eldrichrebello/opqbox2/Schematics/LtSpice/DCDC.asc

C1: cap; 33pF
C2: cap; 330p
C3: cap; 22µF
C4: cap; 100µF
L1: ind; 10µ
R1: res; 649k
R2: res; 162k
R3: res; 10k
R4: res; 15k
R5: res; 15
R6: res; 500k
R7: res; 900k
U1: LTC3534
U2: LT1017
V1: voltage; PWL(0 5 2m 5 3m 3.2 5m 2.7)
V2: voltage; 1.8V
Named nets: 0, Vin, Vout
.tran 0 25m 0
