eldrichrebello/opqbox2/Software/Triggering/src/LocalAnalysis.cpp

#include "LocalAnalysis.hpp"
#include "opqdata.hpp"
#include "Settings.hpp"

#include <math.h>
#include <algorithm>
#include <iostream>
#include <opqdata.hpp>
#include "RedisSerializer.hpp"
#include <boost/log/trivial.hpp>
using namespace opq;
using namespace opq::data;
using namespace std;

LocalAnalysis::LocalAnalysis(opq::data::MeasurementQueue inQ, opq::data::AnalysisQueue outQ) {
    _inQ = inQ;
    _outQ = outQ;
    _state = INITIALIZING_DOWNSAMPLING_FILTER;
    AntialiasDownsamplingFilter_init(&adf);
    LowPassFilter_init(&lpf);
}

void LocalAnalysis::loop(bool &running) {
    auto settings = Settings::Instance();
    float calConstant = settings->getFloat("acquisition_calibration_constant");

    RedisSerializer redis;
    BOOST_LOG_TRIVIAL(info) << "Analysis filter setup....";
    while (running) {
        opq::data::OPQMeasurementPtr measurement = _inQ->pop();
        if (_state != RUNNING) {
            initFilter(measurement);
            continue;
        }
        opq::data::OPQAnalysisPtr analysis = opq::data::make_analysis();
        _downSampled.clear();

        analysis->RMS = 0;
        for (auto &&frame : measurement->cycles) {
            analysis->RMS += rmsVoltage(frame.data);

            for (int i = 0; i < SAMPLES_PER_CYCLE; i++) {
                AntialiasDownsamplingFilter_put(&adf, frame.data[i]);
                if (i % DECIMATION_FACTOR == 0) {
                    float antialiased_value = AntialiasDownsamplingFilter_get(&adf);
                    LowPassFilter_put(&lpf, antialiased_value);
                    _downSampled.push_back(LowPassFilter_get(&lpf));
                }
            }
        }

        analysis->start = measurement->timestamps[0];
        analysis->RMS /= measurement->cycles.size();
        analysis->RMS /= calConstant;

        std::vector<float> zeroCrossings;
        float last = FP_NAN;
        float next = 0;
        for (size_t i = 0; i < _downSampled.size(); i++) {
            if (last != FP_NAN) {
                if ((last <= 0 && _downSampled[i] > 0) || (last < 0 && _downSampled[i] >= 0)) {
                    next = _downSampled[i];
                    zeroCrossings.push_back(1.0f * i - (next) / (next - last));
                }
            }
            last = _downSampled[i];
        }

        float accumulator = 0;
        for (size_t i = 1; i < zeroCrossings.size(); i++) {
            accumulator += zeroCrossings[i] - zeroCrossings[i - 1];
        }
        accumulator /= zeroCrossings.size() - 1;
        analysis->frequency = SAMPLES_PER_CYCLE *
                              CYCLES_PER_SEC /
                              DECIMATION_FACTOR /
                              accumulator;

        analysis->start = measurement->timestamps.front();
        analysis->current_counter = measurement->cycles[measurement->cycles.size() - 1].current_counter;
        analysis->last_gps_counter = measurement->cycles[measurement->cycles.size() - 1].last_gps_counter;
        analysis->flags = 0;
        for (auto &&frame : measurement->cycles) {
            analysis->flags |= frame.flags;
        }
        _outQ->push(analysis);
        redis << measurement;
    }
    BOOST_LOG_TRIVIAL(info) << "Analysis thread done";
}


float LocalAnalysis::rmsVoltage(int16_t data[]) {
    float av = 0;
    for (int i = 0; i < opq::data::SAMPLES_PER_CYCLE; i++) {
        av += 1.0 * data[i] * data[i];
    }
    return sqrtf((float) av / opq::data::SAMPLES_PER_CYCLE);
}


void LocalAnalysis::initFilter(opq::data::OPQMeasurementPtr &m) {
    if (_state == INITIALIZING_DOWNSAMPLING_FILTER) {
        for (auto frame : m->cycles) {
            for (int i = 0; i < opq::data::SAMPLES_PER_CYCLE; i++) {
                AntialiasDownsamplingFilter_put(&adf, frame.data[i]);
                _samplesProcessed++;
            }
        }
        if (_samplesProcessed > ANTIALIASDOWNSAMPLINGFILTER_TAP_NUM) {
            _state = INITIALIZING_LOWPASS_FILTER;
            _samplesProcessed = 0;
        }
    }
    else if (_state == INITIALIZING_LOWPASS_FILTER) {
        for (auto frame : m->cycles) {
            for (int i = 0; i < opq::data::SAMPLES_PER_CYCLE; i++) {
                AntialiasDownsamplingFilter_put(&adf, frame.data[i]);
                if (i % DECIMATION_FACTOR == 0) {
                    LowPassFilter_put(&lpf, AntialiasDownsamplingFilter_get(&adf));
                    _samplesProcessed++;
                }
            }
        }
        if (_samplesProcessed > INITIALIZING_LOWPASS_FILTER) {
            BOOST_LOG_TRIVIAL(info) << "Analysis filters ready";
            _state = RUNNING;
            _samplesProcessed = 0;
        }
    }
}

void LocalAnalysis::calculateFrequency() {

}
